pimlu/gbcam/src/pinout.h

#pragma once

#define BOARD_LED 2

#define GBCAM_START 21
#define GBCAM_SIN 20
#define GBCAM_LOAD 19
#define GBCAM_XCK 22
#define GBCAM_RESET 18
#define GBCAM_READ 25
// no logic level shifter
// #define GBCAM_SHIFT_EN 11
#define GBCAM_VOUT 26

#define GBCAM_VOUT_ADC 0

// sharp - unused right now
#define ENABLE_SHARP 0
